Megumi-desu/sumobot-boccher/Mechanic Design/bracket bener.stl

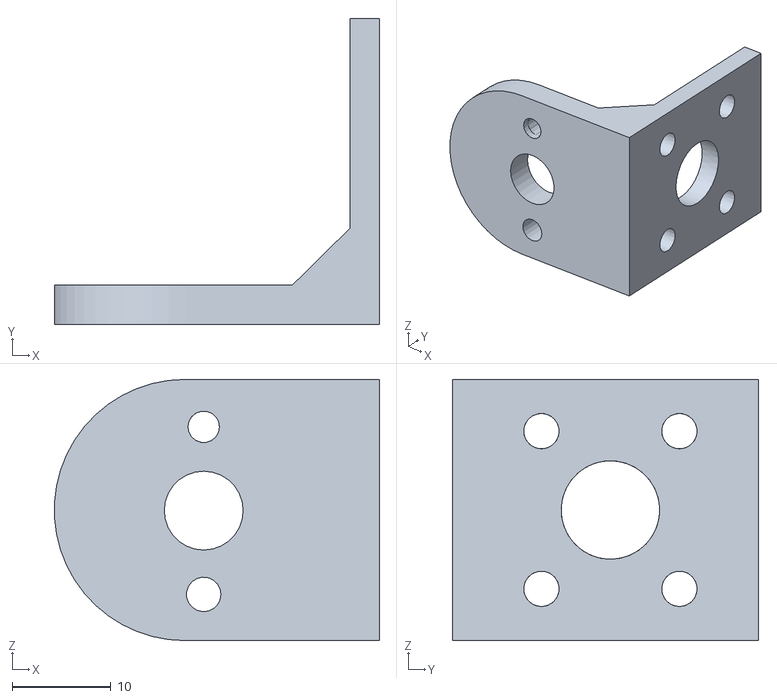
[picture p21: CAD file, 2025-07-30]
Mechanic Design/bracket bener.stl
33.0 x 31.0 x 26.5
