Megumi-desu/sumobot-boccher/Mechanic Design/BTS7960 43A HIGH POWER H BRIDGE MODULE.STEP

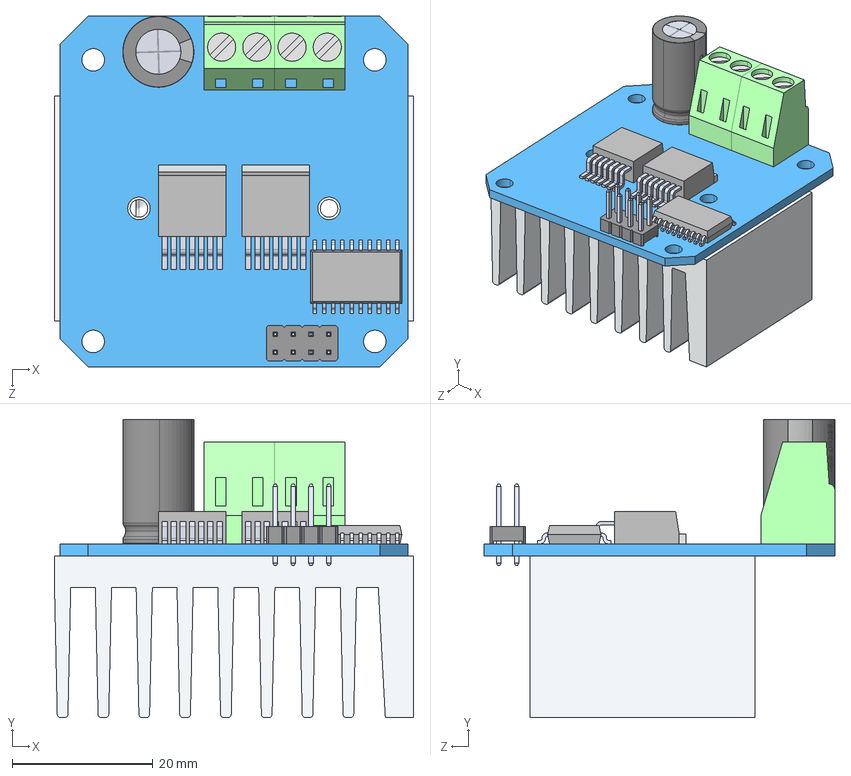
[picture p22: CAD file, 2025-07-30]
Mechanic Design/BTS7960 43A HIGH POWER H BRIDGE MODULE.STEP
51.0 x 42.4 x 49.8 mm
PCB, BTS7960 43A HIGH POWER H BRIDGE MODULE
HEATSINK, BTS7960 43A HIGH POWER H BRIDGE MODULE
ALUMINUM ELECTROLYTIC CAPACITOR, 330 uF, BTS7960 43A HIGH POWER H BRIDGE MODULE
BTN7960 IC, BTS7960 43A HIGH POWER H BRIDGE MODULE x 2
NXP 74HC244D, BUFFER AND LINE DRIVER, BTS7960 43A HIGH POWER H BRIDGE MODULE
8 PIN HEADER, IC, BTS7960 43A HIGH POWER H BRIDGE MODULE
EUROSTYLE TERMINAL BLOCK 2 POS 5.0 MM RA PLUG, BTS7960 43A HIGH POWER H BRIDGE MODULE x 2
