Megumi-desu/sumobot-boccher/Mechanic Design/roda.stl

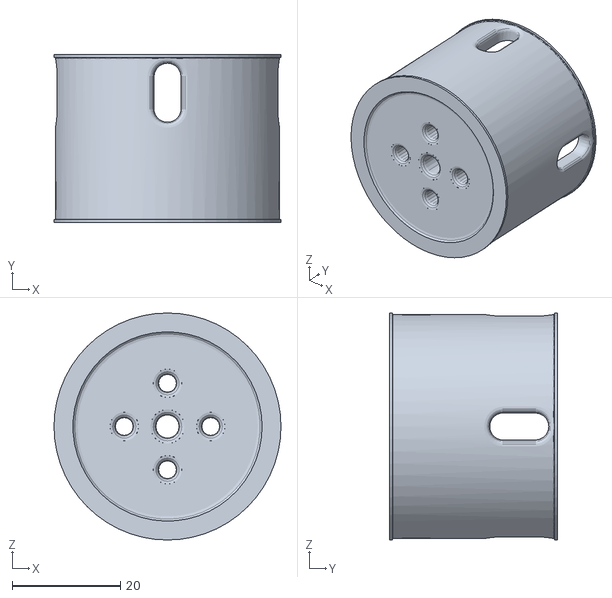
[picture p23: CAD file, 2025-07-30]
Mechanic Design/roda.stl
42.0 x 31.0 x 42.0
