Megumi-desu/sumobot-boccher/Mechanic Design/atap.stl

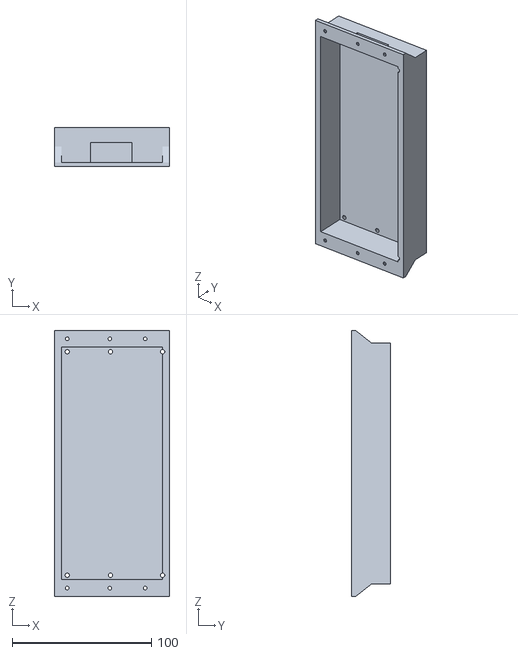
[picture p24: CAD file, 2025-07-30]
Mechanic Design/atap.stl
82.5 x 28.0 x 190.7
