Megumi-desu/sumobot-boccher/Mechanic Design/JGA25-370 .step

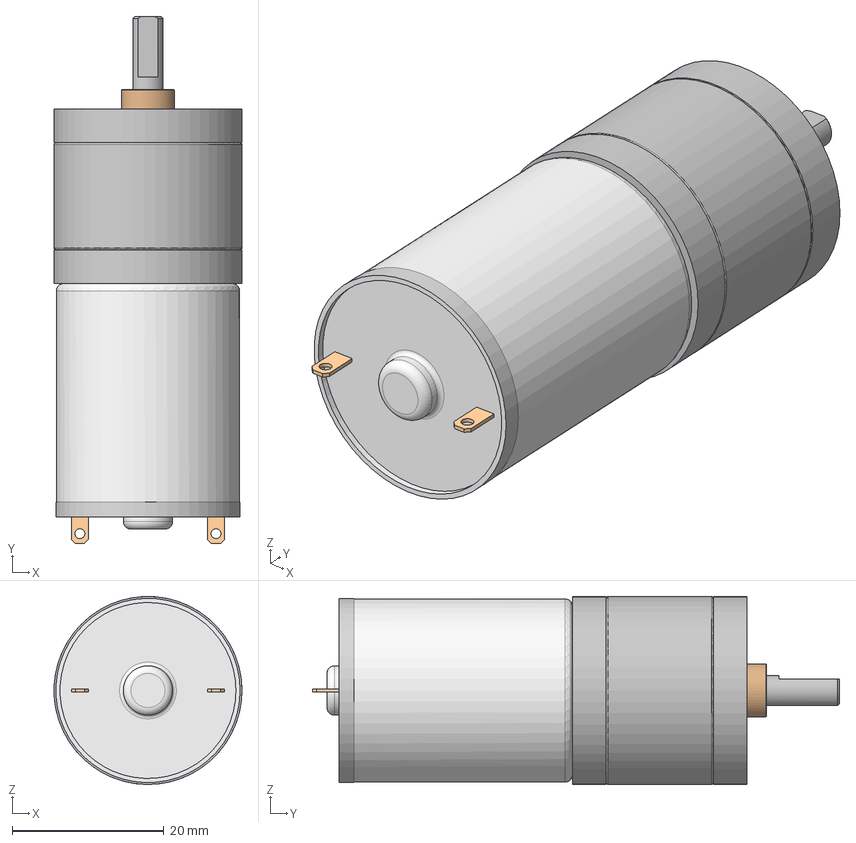
[picture p25: CAD file, 2025-07-30]
Mechanic Design/JGA25-370 .step
24.8 x 69.5 x 24.8 mm
Motor
Gearbox
90116A027_316 Stainless Steel Pan Head Phillips Screws x 2
