Megumi-desu/sumobot-boccher/Mechanic Design/base.stl

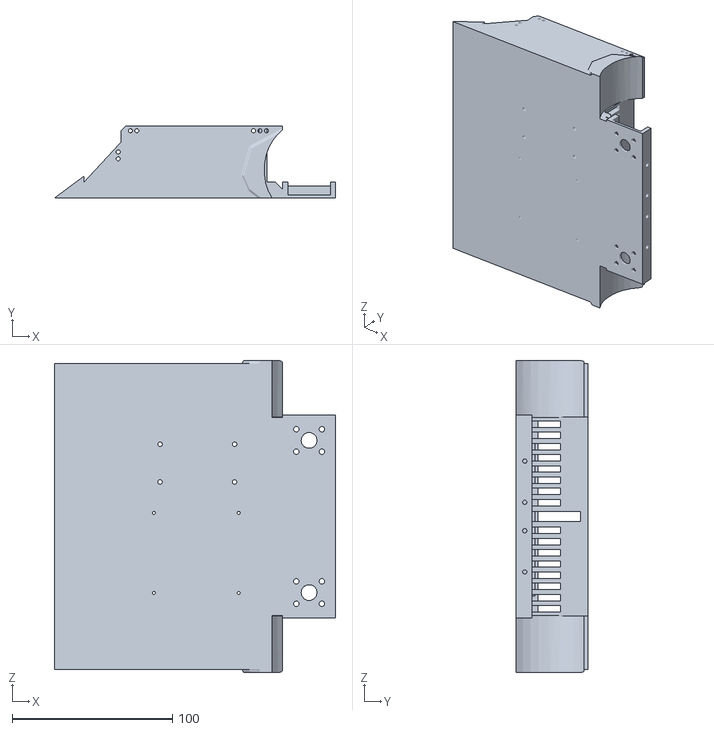
[picture p26: CAD file, 2025-07-30]
Mechanic Design/base.stl
175.4 x 45.0 x 194.7
