Megumi-desu/sumobot-boccher/Mechanic Design/EUROSTYLE TERMINAL BLOCK 2 POS 5.0 MM RA PLUG, BTS7960 43A HIGH POWER H BRIDGE MODULE.SLDPRT

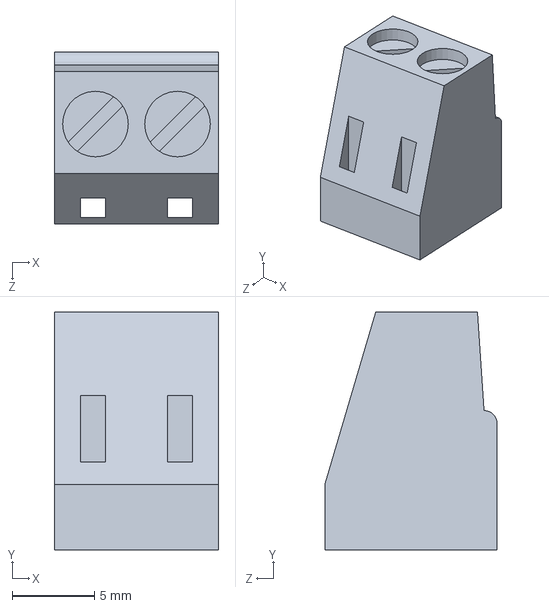
[picture p27: CAD file, 2025-07-30]
Mechanic Design/EUROSTYLE TERMINAL BLOCK 2 POS 5.0 MM RA PLUG, BTS7960 43A HIGH POWER H BRIDGE MODULE.SLDPRT
10.0 x 14.5 x 10.5 mm
